rhomann/kbupgrade/circuits/IBM_M4-1/schematic.sch

## KiCad design circuits/IBM_M4-1/schematic.sch (2009-10-17, an earlier design)

Schematic: schematic.sch

Parts:
C1: 100n
C2, C3: 22p
D1, D2, D3: LED
D4, D5, D6, D7, D8, D9, D10, D11, D12, D13, D14, D15, D16, D17, D18, D19: DIODE
IC1: MEGA32-P; avr-1-DIL40
IC2, IC3: 74HC164
J1: USB_CONN
P1: CONN_19
R1: 10k
R2, R3: 68R
R4: 2k2
R5: 4k7
R6, R7, R8: 470R
X1: 12 MHz

Notes on the sheet:
Diodes are 1N4148.
