rhomann/kbupgrade/circuits/IBM_Model_M/dulcimer.sch

## KiCad design circuits/IBM_Model_M/dulcimer.sch (2009-10-02)

Schematic: dulcimer.sch

Parts:
C1: 100n
C2: 10u
C3, C4: 22p
D1, D2: 3.6V
IC1: MEGA32-P; atmel-DIL40
J1: USB
JP1: PINHD-1X16M; pinhead-1X16M
JP2: PINHD-1X8M; pinhead-1X08M
JP3: PINHD-1X4M; pinhead-1X04M
JP4, JP5, JP6: JUMPER
JP7: PINHD-2X5M; pinhead-2X05M
JP10, JP13: PINHD-1X4; pinhead-1X04
JP11, JP12: PINHD-1X3; pinhead-1X03
P1: CONN_2
R1: 10k
R2: 2k2
R3, R4, R5: 470
R6: 4k7
R7, R8: 68
X1: 12MHz

Notes on the sheet:
USB AUX IN
USB AUX OUT
GND
Keyboard Rows
Keyboard Columns
LEDs
ISP
