rhomann/kbupgrade/circuits/IBM_Model_M_122_keys/schematic.sch

## KiCad design circuits/IBM_Model_M_122_keys/schematic.sch (2010-02-10, an earlier design)

Schematic: schematic.sch

Parts:
C1: 100n
C2, C3: 22p
D1, D2, D3: LED
D4, D5, D6, D7, D8, D9, D10, D11: DIODE
IC1: MEGA32-P; avr-1-DIL40
IC2: 74HC164
J1: USB_CONN
JP1, JP2, JP3: JUMPER
P1: CONN_8
P2: CONN_20
R1: 10k
R2, R3: 68R
R4: 2k2
R5: 4k7
R6, R7, R8: 470R
X1: 12 MHz

Notes on the sheet:
Diodes are 1N4148.
