rhomann/kbupgrade/circuits/IBM_Model_M_122_keys/simple.sch

## KiCad design circuits/IBM_Model_M_122_keys/simple.sch (2010-02-02, an earlier design)

Schematic: simple.sch

Parts:
C1: 100n
C2, C3: 22p
D1, D2: 3.6V
IC1: MEGA32-P; avr-1-DIL40
J1: USB_CONN
JP1, JP2: JUMPER
P1: CONN_8
P2: CONN_20
R1: 10k
R2, R3: 68R
R4: 2k2
R5: 4k7
X1: 12 MHz
