rhomann/kbupgrade/firmware/common/usbfuns.c

/*
 * Keyboard Upgrade -- Firmware for homebrew computer keyboard controllers.
 * Copyright (C) 2009, 2010  Robert Homann
 *
 * Based on RUMP (http://mg8.org/rump/), Copyright (C) 2008  Chris Lee
 *
 * This file is part of the Keyboard Upgrade package.
 *
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
 * You should have received a copy of the GNU General Public License
 * along with the Keyboard Upgrade package; if not, write to the
 * Free Software Foundation, Inc., 51 Franklin Street, Fifth Floor, Boston,
 * MA  02110-1301  USA
 */

#include "eeprom.h"
#include "usbdrv.h"
#include "usbrequests.h"

char PROGMEM usbHidReportDescriptor[USB_CFG_HID_REPORT_DESCRIPTOR_LENGTH]=
{
  0x05, 0x01,   // USAGE_PAGE (Generic Desktop)
  0x09, 0x06,   // USAGE (Keyboard)
  0xa1, 0x01,   // COLLECTION (Application)
  0x05, 0x07,   //   USAGE_PAGE (Keyboard)
  0x19, 0xe0,   //   USAGE_MINIMUM (Keyboard LeftControl)
  0x29, 0xe7,   //   USAGE_MAXIMUM (Keyboard Right GUI)
  0x15, 0x00,   //   LOGICAL_MINIMUM (0)
  0x25, 0x01,   //   LOGICAL_MAXIMUM (1)
  0x75, 0x01,   //   REPORT_SIZE (1)
  0x95, 0x08,   //   REPORT_COUNT (8)
  0x81, 0x02,   //   INPUT (Data,Var,Abs)
  0x95, 0x01,   //   REPORT_COUNT (1)
  0x75, 0x08,   //   REPORT_SIZE (8)
  0x81, 0x03,   //   INPUT (Cnst,Var,Abs)
  0x95, 0x05,   //   REPORT_COUNT (5)
  0x75, 0x01,   //   REPORT_SIZE (1)
  0x05, 0x08,   //   USAGE_PAGE (LEDs)
  0x19, 0x01,   //   USAGE_MINIMUM (Num Lock)
  0x29, 0x05,   //   USAGE_MAXIMUM (Kana)
  0x91, 0x02,   //   OUTPUT (Data,Var,Abs)
  0x95, 0x01,   //   REPORT_COUNT (1)
  0x75, 0x03,   //   REPORT_SIZE (3)
  0x91, 0x03,   //   OUTPUT (Cnst,Var,Abs)
  0x95, 0x06,   //   REPORT_COUNT (6)
  0x75, 0x08,   //   REPORT_SIZE (8)
  0x15, 0x00,   //   LOGICAL_MINIMUM (0)
  0x25, 0x65,   //   LOGICAL_MAXIMUM (101)
  0x05, 0x07,   //   USAGE_PAGE (Keyboard)
  0x19, 0x00,   //   USAGE_MINIMUM (Reserved (no event indicated))
  0x29, 0x65,   //   USAGE_MAXIMUM (Keyboard Application)
  0x81, 0x00,   //   INPUT (Data,Ary,Abs)
  0xc0          // END_COLLECTION
};

typedef struct
{
  uint8_t modifiers;
  uint8_t reserved;
  uint8_t keys[6];
} Report;

static Report usb_report_buffer;
static uchar usb_protocol_ver_buffer;
static uchar usb_idle_rate;
static uchar usb_expect_report;

/* This union is used to work around warnings that are thrown when casting
 * const pointers to non-const. */
static union
{
  const uint8_t *constptr;
  uint8_t *ptr;
} copy_data_ptr;

static uint8_t copy_data_len;

static usbMsgLen_t handle_request(const usbRequest_t *rq)
{
  static uint8_t buffer[8];

  usbMsgPtr=(void *)buffer;
  switch(rq->bRequest)
  {
   case KURQ_GET_HWINFO:
    ((KBHwinfo *)buffer)->max_mapindex=MAXIMUM_KEYMAP_INDEX;
    ((KBHwinfo *)buffer)->current_mapindex=get_current_keymap_index(0);
    ((KBHwinfo *)buffer)->num_of_keys=NUM_OF_KEYS;
    ((KBHwinfo *)buffer)->num_of_rows=NUM_OF_ROWS;
    ((KBHwinfo *)buffer)->num_of_cols=NUM_OF_COLUMNS;
    ((KBHwinfo *)buffer)->matrix_bvlen=MATRIX_BITVECTOR_LEN;
    return sizeof(KBHwinfo);
   case KURQ_GET_LAYOUT:
    usb_expect_report=KURQ_GET_DATA_FROM_PGM;
    copy_data_ptr.constptr=matrix_bits;
    copy_data_len=MATRIX_BITVECTOR_LEN;
    return USB_NO_MSG;
   case KURQ_GET_KEYMAP:
    if(rq->wValue.bytes[0] == 0)
    {
      /* read default key map from flash memory */
      usb_expect_report=KURQ_GET_DATA_FROM_PGM;
      copy_data_ptr.constptr=(const uint8_t *)&standard_stored_keymap;
    }
    else if(rq->wValue.bytes[0] <= MAXIMUM_KEYMAP_INDEX)
    {
      /* read user-defined key map from EEPROM */
      usb_expect_report=KURQ_GET_DATA_FROM_EEPROM;
      copy_data_ptr.constptr=KEYMAP_POINTER_FROM_INDEX(rq->wValue.bytes[0]);
    }
    else return 0;
    copy_data_len=sizeof(Storedmap);
    return USB_NO_MSG;
   case KURQ_SET_KEYMAP:
    if(rq->wValue.bytes[0] == 0 || rq->wValue.bytes[0] > MAXIMUM_KEYMAP_INDEX)
      return 0;
    uint8_t *loc=KEYMAP_POINTER_FROM_INDEX(rq->wValue.bytes[0]);
    if(rq->wValue.bytes[1] == 0)
    {
      /* write data sent by host */
      usb_expect_report=KURQ_WRITE_DATA_TO_EEPROM;
      copy_data_ptr.ptr=loc;
      copy_data_len=sizeof(Storedmap);
      return USB_NO_MSG;
    }
    else
    {
      /* just delete the entry */
      eeprom_write_byte(loc,0xff);
      return 0;
    }
   case KURQ_RESET:
    /* loop "endlessly" for ~0.5s */
    WDTCR=
#ifdef WDTOE
      _BV(WDTOE)|
#else /* !WDTOE */
      _BV(WDCE)|
#endif /* WDTOE */
      _BV(WDE)|_BV(WDP2)|_BV(WDP0);
    while(1);
   default:
    return 0;
  }
}

usbMsgLen_t usbFunctionSetup(uchar data[8])
{
  usbRequest_t *rq=(void *)data;
  usbMsgPtr=(void *)&usb_report_buffer;

  if((rq->bmRequestType&USBRQ_TYPE_MASK) != USBRQ_TYPE_CLASS)
  {
    if((rq->bmRequestType&USBRQ_TYPE_MASK) == USBRQ_TYPE_VENDOR)
      return handle_request(rq);
    return 0;
  }

  switch(rq->bRequest)
  {
   case USBRQ_HID_GET_REPORT:
    return sizeof(usb_report_buffer);
   case USBRQ_HID_GET_IDLE:
    usbMsgPtr=&usb_idle_rate;
    return 1;
   case USBRQ_HID_GET_PROTOCOL:
    if(rq->wValue.bytes[1] < 1) usb_protocol_ver_buffer=rq->wValue.bytes[1];
    return 0;
   case USBRQ_HID_SET_REPORT:
    if(rq->wLength.word == 1)
    {
      usb_expect_report=USBRQ_HID_SET_REPORT;
      return USB_NO_MSG;
    }
    return 0;
   case USBRQ_HID_SET_IDLE:
    usb_idle_rate=rq->wValue.bytes[1];
    return 0;
   case USBRQ_HID_SET_PROTOCOL:
    usbMsgPtr=&usb_protocol_ver_buffer;
    return 1;
   default:
    return 0;
  }
}

uchar usbFunctionWrite(uchar *data, uchar len)
{
  uchar ret=0;

  switch(usb_expect_report)
  {
#ifdef USB_SET_LED_STATE
   case USBRQ_HID_SET_REPORT:
    USB_SET_LED_STATE(data[0]);
    ret=1;
    break;
#endif /* USB_SET_LED_STATE */
   case KURQ_WRITE_DATA_TO_EEPROM:
    if(copy_data_len < len) ret=copy_data_len;
    else                    ret=len;
    eeprom_write_block(data,copy_data_ptr.ptr,ret);
    copy_data_ptr.ptr+=ret;
    copy_data_len-=ret;
    if(copy_data_len > 0) return ret;
    break;
  }

  usb_expect_report=0;
  return ret;
}

uchar usbFunctionRead(uchar *data, uchar len)
{
  uchar ret=0;

  switch(usb_expect_report)
  {
   case KURQ_GET_DATA_FROM_PGM:
   case KURQ_GET_DATA_FROM_EEPROM:
    if(copy_data_len < len) ret=copy_data_len;
    else                    ret=len;
    if(usb_expect_report == KURQ_GET_DATA_FROM_PGM)
      memcpy_P(data,copy_data_ptr.constptr,ret);
    else
      eeprom_read_block(data,copy_data_ptr.constptr,ret);
    copy_data_ptr.constptr+=ret;
    copy_data_len-=ret;
    if(copy_data_len > 0) return ret;
    break;
   default:
    break;
  }

  usb_expect_report=0;
  return ret;
}

#ifdef USB_SET_LED_STATE
#undef USB_SET_LED_STATE
#endif /* USB_SET_LED_STATE */
