rhomann/kbupgrade/firmware/common/keymapdecode.c

/*
 * Keyboard Upgrade -- Firmware for homebrew computer keyboard controllers.
 * Copyright (C) 2009, 2010  Robert Homann
 *
 * This file is part of the Keyboard Upgrade package.
 *
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
 * You should have received a copy of the GNU General Public License
 * along with the Keyboard Upgrade package; if not, write to the
 * Free Software Foundation, Inc., 51 Franklin Street, Fifth Floor, Boston,
 * MA  02110-1301  USA
 */

#ifdef __AVR_ARCH__
#include "eeprom.h"
#endif /* __AVR_ARCH__ */

#ifdef NO_GHOSTKEY_PREVENTION
#ifndef NO_ENHANCED_GKP
#define NO_ENHANCED_GKP 1
#endif /* !NO_ENHANCED_GKP */
#endif /* NO_GHOSTKEY_PREVENTION */

static void decode(Map *map, const uint8_t *src, uint8_t from_eeprom)
{
#ifndef __AVR_ARCH__
#define pgm_read_byte(PTR)     (*(PTR))
#define eeprom_read_byte(PTR)  (*(PTR))
#endif /* !__AVR_ARCH__ */

  memset(map,0,sizeof(Map));

#ifndef NO_ENHANCED_GKP
  memset(column_valid_mask,0xff,sizeof(Columnstate)*NUM_OF_ROWS);
#endif /* !NO_ENHANCED_GKP */

  int keys_left=NUM_OF_KEYS;
  uint8_t mask=0x80;
  const uint8_t *ptr=matrix_bits;
  uint8_t bits=pgm_read_byte(ptr);

#ifndef NO_ENHANCED_GKP
  Columnstate cmask=(Columnstate)(COLUMNSTATE_EMPTY << 1);
  uint8_t columns=NUM_OF_COLUMNS, row=0;
#endif /* !NO_ENHANCED_GKP */

  for(uint8_t *dest=(void *)map->mat; keys_left > 0; ++dest)
  {
    if(bits&mask)
    {
      if(from_eeprom) *dest=eeprom_read_byte(src);
      else            *dest=pgm_read_byte(src);
      ++src;
#ifdef ZERO_CODES_ARE_TRASH_CODES
      if(*dest == 0) *dest=KEY_trash;
#endif /* ZERO_CODES_ARE_TRASH_CODES */
#ifndef NO_ENHANCED_GKP
      column_valid_mask[row]&=cmask;
#endif /* !NO_ENHANCED_GKP */
      --keys_left;
    }
    if((uint8_t)(mask>>=1) == 0)
    {
      ++ptr;
      bits=pgm_read_byte(ptr);
      mask=0x80;
    }
#ifndef NO_ENHANCED_GKP
    if(--columns)
    {
      cmask=(cmask << 1)|1;
    }
    else
    {
      cmask=(Columnstate)(COLUMNSTATE_EMPTY << 1);
      columns=NUM_OF_COLUMNS;
      ++row;
    }
#endif /* !NO_ENHANCED_GKP */
  }
}

#ifdef __AVR_ARCH__
static uint8_t get_current_keymap_index(uint8_t fnkey)
{
  if(!(CFG_KEYMAP0_PORT&_BV(CFG_KEYMAP0_PIN)) || fnkey > 3)
  {
    /* locked at index 0 via jumper */
    return 0;
  }

  return eeprom_read_byte(&CONFIG_POINTER->keymap_indices[fnkey]);
}

static void write_current_keymap_index(uint8_t fnkey, uint8_t idx)
{
  if(fnkey > 3) return;
  if(eeprom_read_byte(&CONFIG_POINTER->keymap_indices[fnkey]) != idx)
    eeprom_write_byte(&CONFIG_POINTER->keymap_indices[fnkey],idx);
}

static const void *get_eeprom_keymap_pointer(uint8_t idx)
{
  if(idx == 0 || idx > MAXIMUM_KEYMAP_INDEX) return KEYMAP_POINTER_NULL;

  const uint8_t *ptr=KEYMAP_POINTER_FROM_INDEX(idx);
  uint8_t temp=eeprom_read_byte(ptr);
  if(temp == 0x00 || temp == 0xff) return KEYMAP_POINTER_NULL;
  return ptr+KEYMAP_NAME_LENGTH;
}

static void set_current_keymap(uint8_t idx, char permanent_switch)
{
  const uint8_t *mapptr=KEYMAP_POINTER_NULL;

  if(idx > 0) mapptr=get_eeprom_keymap_pointer(idx);

  if(mapptr == KEYMAP_POINTER_NULL)
  {
    idx=0;
    mapptr=standard_stored_keymap.codes;
  }

  if(permanent_switch) write_current_keymap_index(0,idx);
  decode(&current_keymap,mapptr,idx);
}
#endif /* __AVR_ARCH__ */
