rhomann/kbupgrade/firmware/common/scanrows.c

/*
 * Keyboard Upgrade -- Firmware for homebrew computer keyboard controllers.
 * Copyright (C) 2009, 2010  Robert Homann
 *
 * This file is part of the Keyboard Upgrade package.
 *
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
 * You should have received a copy of the GNU General Public License
 * along with the Keyboard Upgrade package; if not, write to the
 * Free Software Foundation, Inc., 51 Franklin Street, Fifth Floor, Boston,
 * MA  02110-1301  USA
 */

#if !(defined ROWS_DDR1 && defined ROWS_PORT1)
#error Please define ROWS_DDR1 and ROWS_PORT1.
#endif

#if NUM_OF_ROWS > 8
#if !(defined ROWS_DDR2 && defined ROWS_PORT2)
#error Please define ROWS_DDR2 and ROWS_PORT2.
#endif
#endif

#ifdef NO_GHOSTKEY_PREVENTION
#ifndef NO_ENHANCED_GKP
#define NO_ENHANCED_GKP 1
#endif /* !NO_ENHANCED_GKP */
#endif /* NO_GHOSTKEY_PREVENTION */

/*
 * Update global array column_states with values read from the I/O pins.
 */
static char update_column_states(void)
{
  char state_changed=0;

#if NUM_OF_ROWS > 8
  ROWS_DDR2=0x00;
  ROWS_PORT2=0xff;
#endif /* NUM_OF_ROWS > 8 */

#if NUM_OF_ROWS > 16
  deactivate_high_rows();
#endif /* NUM_OF_ROWS > 16 */

  /* The loop iterates over all row pins; in each iteration one of the pins is
   * configured as output pin, whereas the others are left as inputs with their
   * pull-ups enabled. The output pin is set to 0 so that it pulls down the
   * activated colums (column pins are configured as inputs with pull-ups
   * enabled). */
  for(uint8_t row=0; row < NUM_OF_ROWS; ++row)
  {
#if NUM_OF_ROWS > 8
    if(row == 8)
    {
      ROWS_DDR1=0x00;
      ROWS_PORT1=0xff;
    }

#if NUM_OF_ROWS > 16
    else if(row == 16)
    {
      ROWS_DDR2=0x00;
      ROWS_PORT2=0xff;
    }
#endif /* NUM_OF_ROWS > 16 */

    if(row < 8)
    {
#endif /* NUM_OF_ROWS > 8 */
      ROWS_DDR1=_BV(row);
      ROWS_PORT1=~_BV(row);
#if NUM_OF_ROWS > 8
    }
    else
#if NUM_OF_ROWS > 16
    if(row < 16)
#endif /* NUM_OF_ROWS > 16 */
    {
      ROWS_DDR2=_BV(row&0x07);
      ROWS_PORT2=~_BV(row&0x07);
    }
#if NUM_OF_ROWS > 16
    else
    {
      /* The code above assumes that the first 16 rows are activated using two
       * ports that are used exclusively for this task. Having more than 16
       * rows means that we'll have to use some pins from ports that are used
       * for other purposes already, but at this point we don't know which pins
       * they are. This inline function comes to a rescue. */
      activate_high_row(row);
    }
#endif /* NUM_OF_ROWS > 16 */
#endif /* NUM_OF_ROWS > 8 */

    _delay_us(30);

#ifdef COLS_PIN
    Columnstate cols=COLS_PIN;
#else /* !COLS_PIN */
    Columnstate cols=read_columns();
#endif /* COLS_PIN */

#ifndef NO_ENHANCED_GKP
    cols|=column_valid_mask[row];
#endif /* !NO_ENHANCED_GKP */
    if(column_states[row] != cols)
    {
      column_states[row]=cols;
      state_changed=1;
    }
  }

  return state_changed;
}
